emeb/S3GTA/Software/main/audio.h

/*
 * audio.h - audio via I2S.
 * 03-9-22 E. Brombaugh
 */

#ifndef __audio__
#define __audio__

extern uint64_t audio_load[3];
esp_err_t audio_init(void);
void audio_mute(uint8_t enable);
int16_t audio_get_level(uint8_t idx);

#endif
