emeb/S3GTA/Software/main/fx_filters.h

/*
 * fx_filters.h -  various 4th-order filters for F373 Mod
 * 03-29-20 E. Brombaugh
 */

#ifndef __fx_filters__
#define __fx_filters__

#include "fx.h"

extern fx_struct fx_lpf_struct;
extern fx_struct fx_hpf_struct;
extern fx_struct fx_bpf_struct;

#endif
